Westsi/ESP-Smartwatch/smartwatch_code/images/png/add_160.png

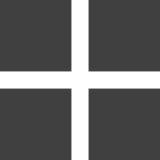
smartwatch_code/images/png/add_160.png
