Westsi/ESP-Smartwatch/smartwatch_code/images/png/ecgheart_160.png

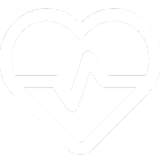
smartwatch_code/images/png/ecgheart_160.png
