Westsi/ESP-Smartwatch/smartwatch_code/images/png/notifications_160.png

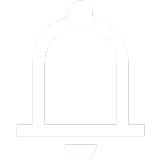
smartwatch_code/images/png/notifications_160.png
