Westsi/ESP-Smartwatch/smartwatch_code/images/png/pool_160.png

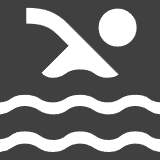
smartwatch_code/images/png/pool_160.png
