Westsi/ESP-Smartwatch/smartwatch_code/images/png/remove_160.png

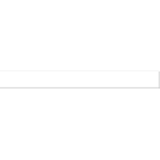
smartwatch_code/images/png/remove_160.png
