Westsi/ESP-Smartwatch/smartwatch_code/images/png/settings_160.png

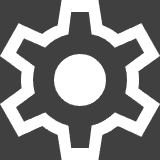
smartwatch_code/images/png/settings_160.png
