Westsi/ESP-Smartwatch/smartwatch_code/images/png/skipnext_160.png

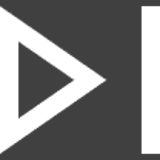
smartwatch_code/images/png/skipnext_160.png
