Westsi/ESP-Smartwatch/smartwatch_code/images/png/skipprevious_160.png

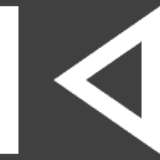
smartwatch_code/images/png/skipprevious_160.png
