Westsi/ESP-Smartwatch/smartwatch_code/images/png/Spotify_160.png

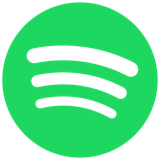
smartwatch_code/images/png/Spotify_160.png
