Westsi/ESP-Smartwatch/smartwatch_code/images/png/tennis_160.png

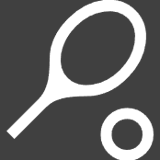
smartwatch_code/images/png/tennis_160.png
