Westsi/ESP-Smartwatch/smartwatch_code/images/png/steps_160.png

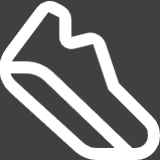
smartwatch_code/images/png/steps_160.png
