Westsi/ESP-Smartwatch/smartwatch_code/include/devicepins.h

#ifndef DEVICE_PINS_H_
#define DEVICE_PINS_H_

#define MPU_SDA 32
#define MPU_SCL 33

#define CASE_BUTTON 4

#define SD_CS 15
#define SD_MOSI 13
#define SD_MISO 12
#define SD_CLK 14

#define SCREEN_CLK 18
#define SCREEN_MISO 19
#define SCREEN_MOSI 23

#define TOUCH_SDA 21
#define TOUCH_SCL 22


#endif
